tbernard0-GTA/lampform-lab/dist/downloads/reserve_medium/README.txt

LampForm Lab v0.5 / Reserve Medium
Both-part print gate: False
Reserve Medium: abertura equivalente média 6.65 mm; material projetado +12.7%; geometria plana alterada 16.6%. P95 36.0 → 34.3%; P99 45.3 → 48.8%; pico 64.3 → 80.8%; críticos 45 → 44. Gates: TRADE-OFF.
Reserve Medium: abertura equivalente média 6.74 mm; material projetado +8.9%; geometria plana alterada 12.4%. P95 55.5 → 50.9%; P99 70.1 → 79.4%; pico 83.9 → 87.0%; críticos 98 → 93. Gates: PASS.
Units mm. Flat lattice 1 mm, original rim 4 mm. Inspect layers in your slicer. Relative geometric model, not calibrated polymer strain. Mold and Push unchanged. Original source meshes have duplicated faces and are not watertight.
