tbernard0-GTA/lampform-lab/dist/downloads/reserve_search_1/README.txt

LampForm Lab v0.5 / Reserve Search 1
Both-part print gate: False
Reserve Search 1: abertura equivalente média 6.90 mm; material projetado +1.3%; geometria plana alterada 2.7%. P95 36.0 → 32.7%; P99 45.3 → 37.8%; pico 64.3 → 63.0%; críticos 45 → 34. Gates: PASS.
Reserve Search 1: abertura equivalente média 6.91 mm; material projetado +1.0%; geometria plana alterada 2.2%. P95 55.5 → 54.5%; P99 70.1 → 69.9%; pico 83.9 → 84.0%; críticos 98 → 100. Gates: TRADE-OFF.
Units mm. Flat lattice 1 mm, original rim 4 mm. Inspect layers in your slicer. Relative geometric model, not calibrated polymer strain. Mold and Push unchanged. Original source meshes have duplicated faces and are not watertight.
