tbernard0-GTA/lampform-lab/dist/downloads/reserve_search_2/README.txt

LampForm Lab v0.5 / Reserve Search 2
Both-part print gate: False
Reserve Search 2: abertura equivalente média 6.88 mm; material projetado +2.4%; geometria plana alterada 4.2%. P95 36.0 → 35.5%; P99 45.3 → 46.5%; pico 64.3 → 66.9%; críticos 45 → 43. Gates: PASS.
Reserve Search 2: abertura equivalente média 6.89 mm; material projetado +1.7%; geometria plana alterada 3.3%. P95 55.5 → 53.9%; P99 70.1 → 70.3%; pico 83.9 → 85.5%; críticos 98 → 98. Gates: TRADE-OFF.
Units mm. Flat lattice 1 mm, original rim 4 mm. Inspect layers in your slicer. Relative geometric model, not calibrated polymer strain. Mold and Push unchanged. Original source meshes have duplicated faces and are not watertight.
