tbernard0-GTA/lampform-lab/dist/downloads/reserve_search_3/README.txt

LampForm Lab v0.5 / Reserve Search 3
Both-part print gate: True
Reserve Search 3: abertura equivalente média 6.77 mm; material projetado +7.6%; geometria plana alterada 10.9%. P95 36.0 → 29.7%; P99 45.3 → 32.2%; pico 64.3 → 35.1%; críticos 45 → 10. Gates: PASS.
Reserve Search 3: abertura equivalente média 6.82 mm; material projetado +5.3%; geometria plana alterada 8.1%. P95 55.5 → 50.6%; P99 70.1 → 71.2%; pico 83.9 → 84.6%; críticos 98 → 97. Gates: PASS.
Units mm. Flat lattice 1 mm, original rim 4 mm. Inspect layers in your slicer. Relative geometric model, not calibrated polymer strain. Mold and Push unchanged. Original source meshes have duplicated faces and are not watertight.
