tbernard0-GTA/lampform-lab/dist/media/comparisons/peca-1-A_uniform.png

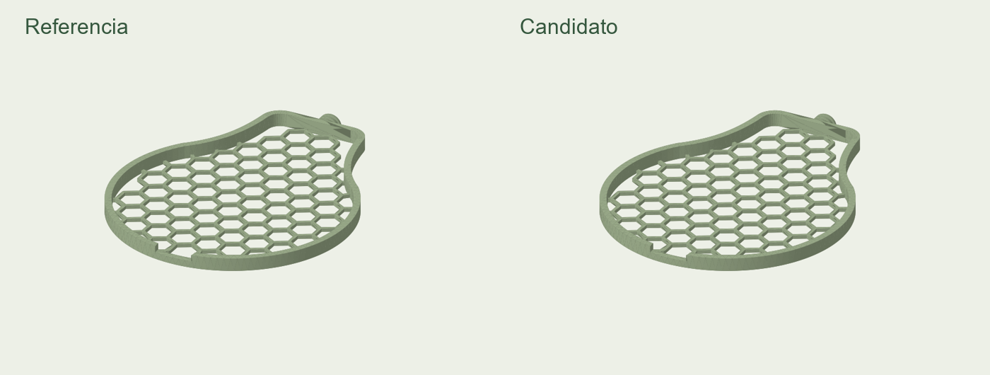
dist/media/comparisons/peca-1-A_uniform.png
