tbernard0-GTA/lampform-lab/dist/media/comparisons/peca-2-A_uniform.png

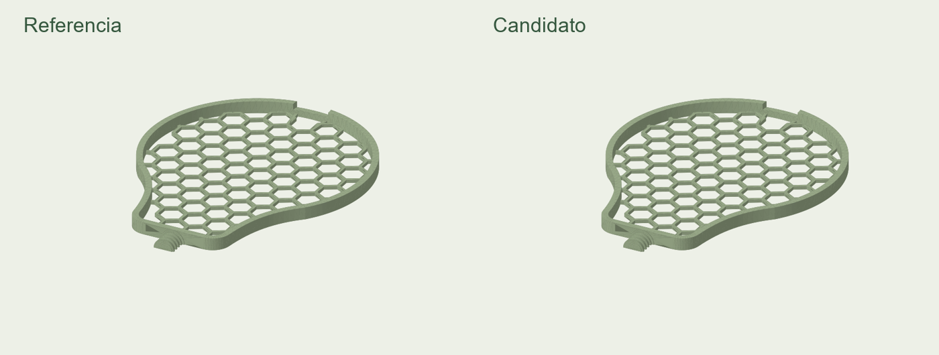
dist/media/comparisons/peca-2-A_uniform.png
