tbernard0-GTA/lampform-lab/docs/video_frames/01_object.png

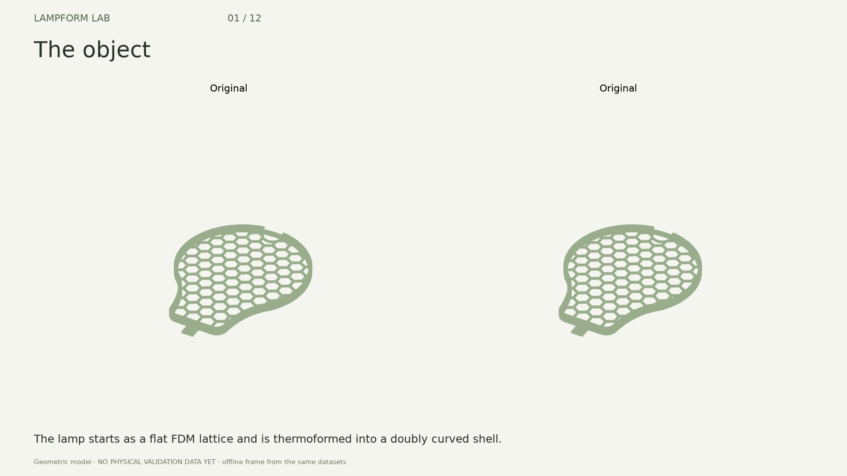
docs/video_frames/01_object.png
