tbernard0-GTA/lampform-lab/docs/video_frames/05_forming.png

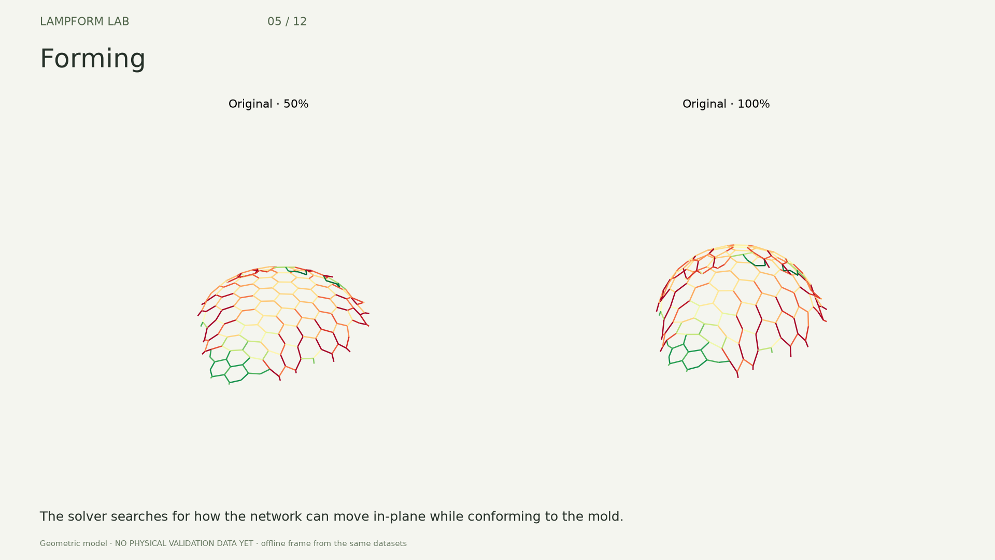
docs/video_frames/05_forming.png
