tbernard0-GTA/lampform-lab/docs/video_frames/06_principal_stretch.png

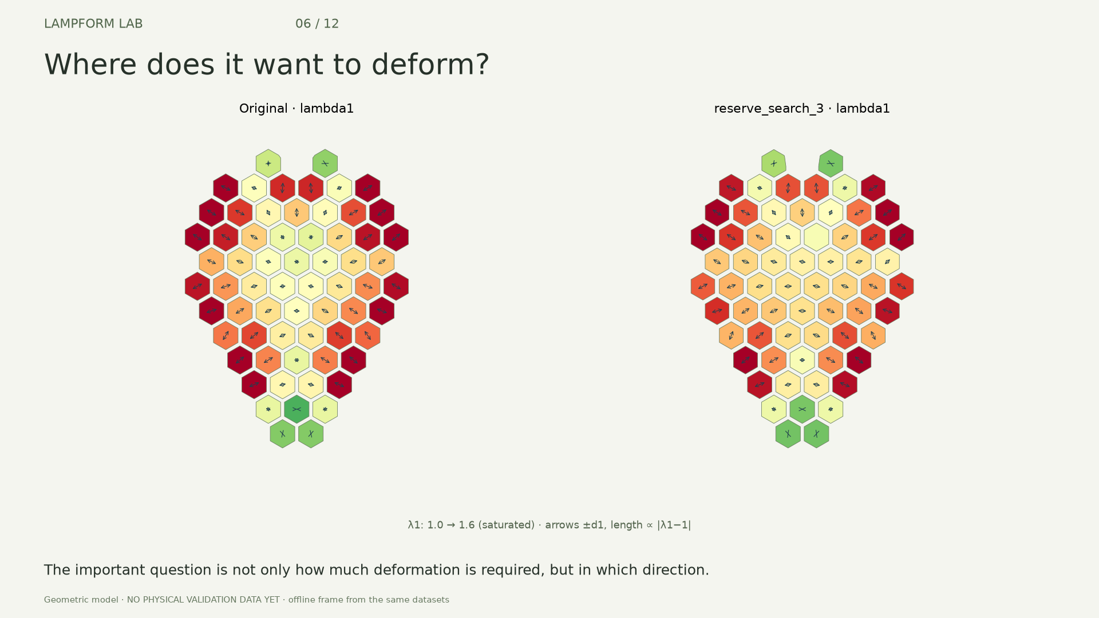
docs/video_frames/06_principal_stretch.png
