tbernard0-GTA/lampform-lab/docs/video_frames/07_mechanisms.png

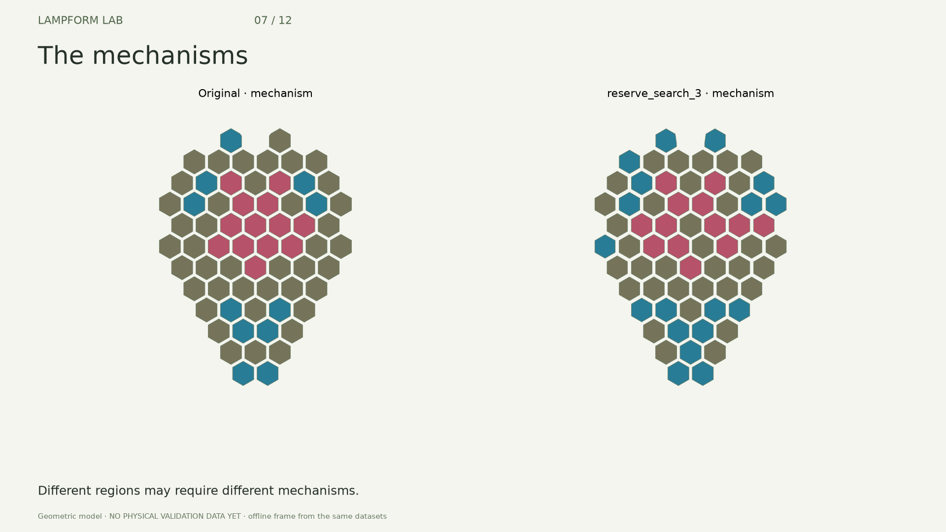
docs/video_frames/07_mechanisms.png
