tbernard0-GTA/lampform-lab/docs/video_frames/12_loop.png

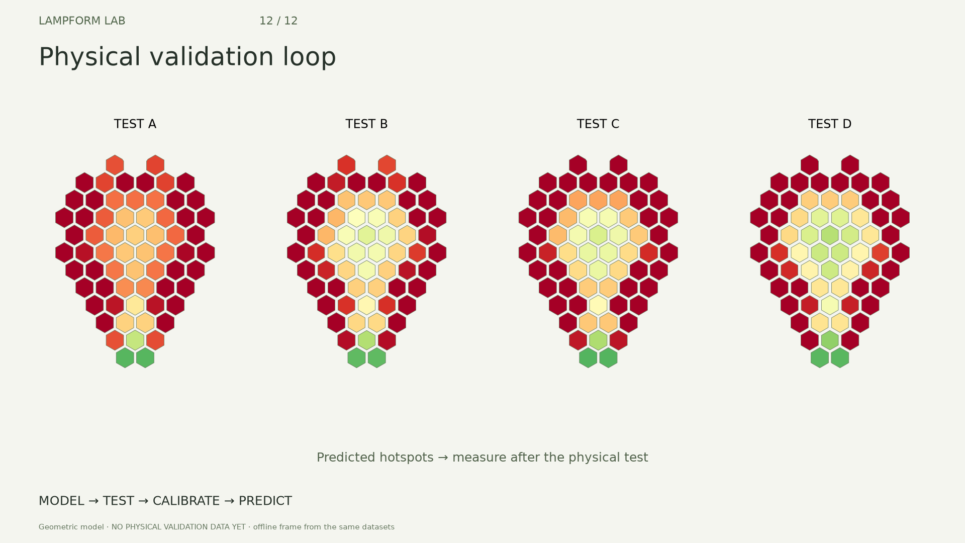
docs/video_frames/12_loop.png
