tbernard0-GTA/lampform-lab/dist/downloads/hybrid_high/HAB-2.stl

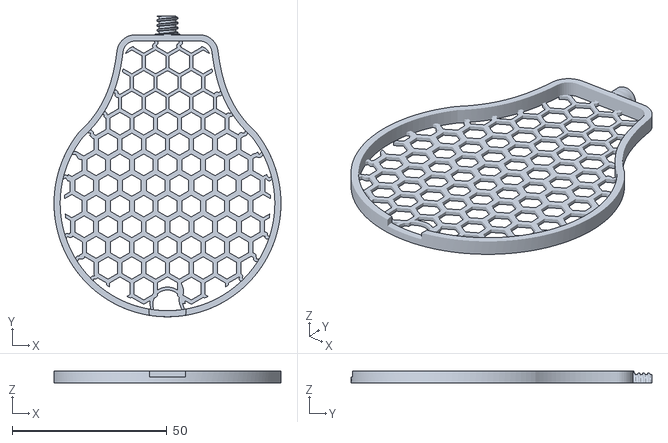
[picture p21: CAD file, 2026-09-14]
dist/downloads/hybrid_high/HAB-2.stl
73.3 x 97.1 x 4.00
