tbernard0-GTA/lampform-lab/dist/downloads/peca-2/peca-2-uniform-w8-h12.stl

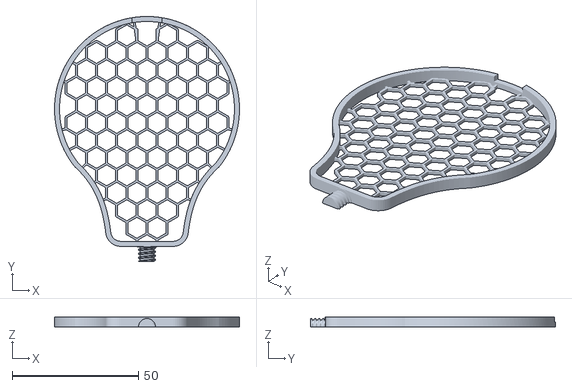
[picture p22: CAD file, 2026-09-14]
dist/downloads/peca-2/peca-2-uniform-w8-h12.stl
73.3 x 97.1 x 4.00
