tbernard0-GTA/lampform-lab/dist/downloads/peca-1/peca-1-uniform-w8-h8.stl

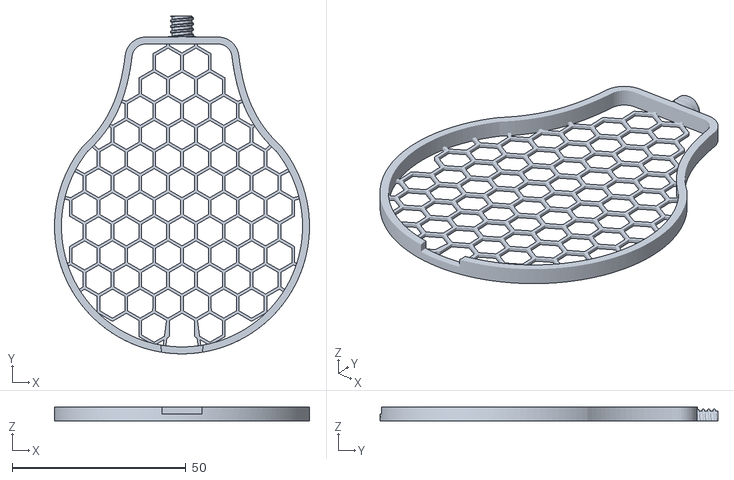
[picture p23: CAD file, 2026-09-14]
dist/downloads/peca-1/peca-1-uniform-w8-h8.stl
73.3 x 97.1 x 4.00
