tbernard0-GTA/lampform-lab/dist/downloads/peca-1/peca-1-comply.stl

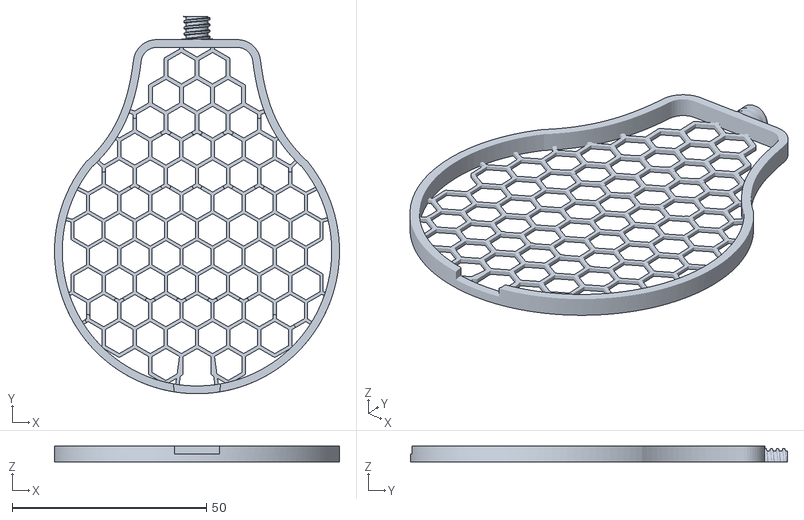
[picture p25: CAD file, 2026-09-14]
dist/downloads/peca-1/peca-1-comply.stl
73.3 x 97.1 x 4.00
