tbernard0-GTA/lampform-lab/dist/downloads/physical-test-v1/ORIGINAL_SUBMERGED.stl

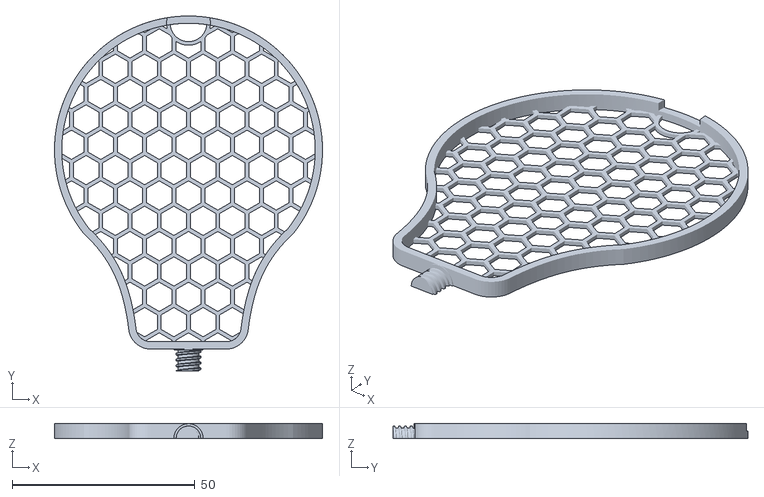
[picture p27: CAD file, 2026-09-14]
dist/downloads/physical-test-v1/ORIGINAL_SUBMERGED.stl
73.3 x 97.1 x 4.00
