tbernard0-GTA/lampform-lab/dist/downloads/peca-1/peca-1-triangle-uniform.stl

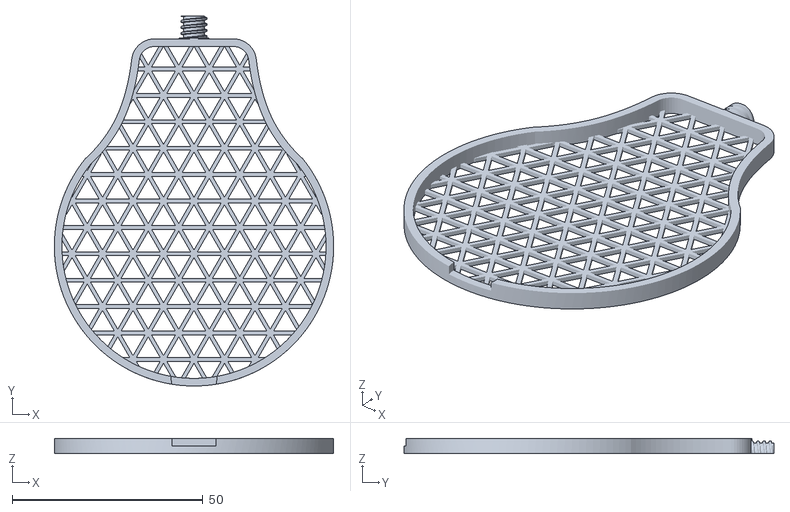
[picture p28: CAD file, 2026-09-14]
dist/downloads/peca-1/peca-1-triangle-uniform.stl
73.3 x 97.1 x 4.00
