tbernard0-GTA/lampform-lab/dist/downloads/peca-1/molde-peca-1.stl

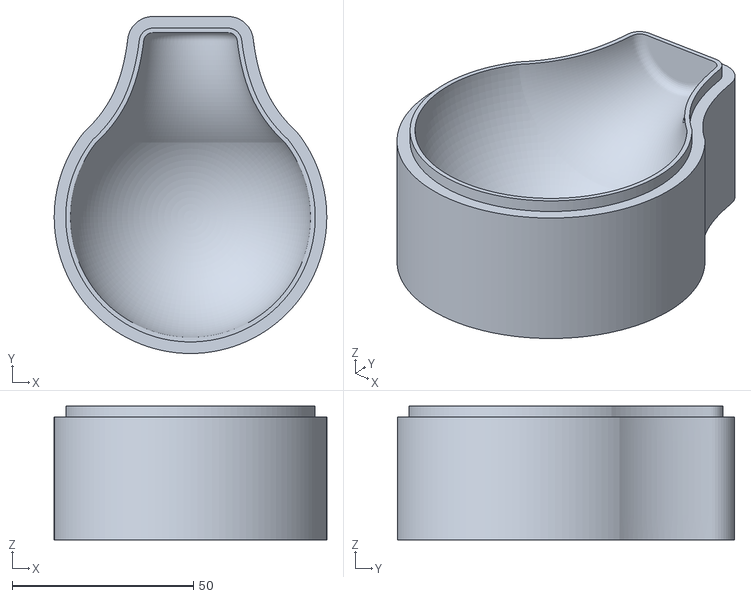
[picture p29: CAD file, 2026-09-14]
dist/downloads/peca-1/molde-peca-1.stl
75.3 x 93.1 x 37.0
