tbernard0-GTA/lampform-lab/dist/downloads/peca-2/molde-peca-2.stl

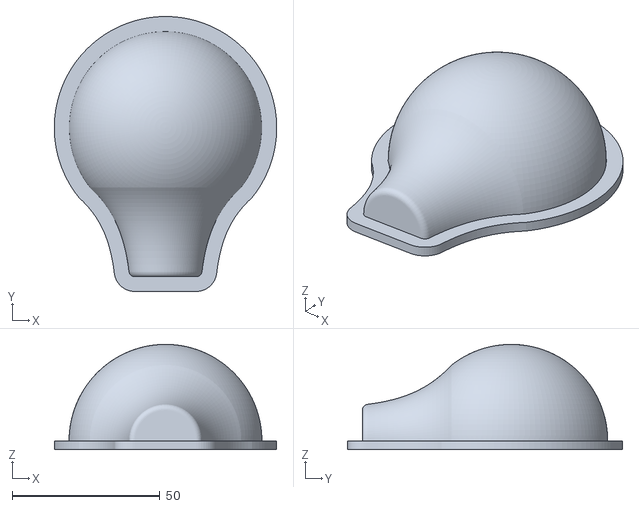
[picture p30: CAD file, 2026-09-14]
dist/downloads/peca-2/molde-peca-2.stl
75.3 x 93.1 x 35.6
