tbernard0-GTA/lampform-lab/docs/video_frames/04_reconstruction.png

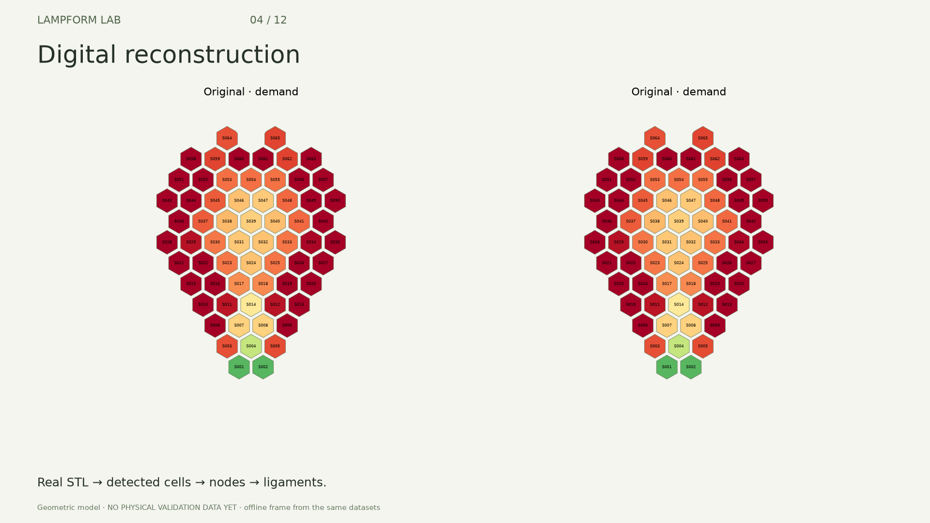
docs/video_frames/04_reconstruction.png
