tbernard0-GTA/lampform-lab/legacy/lampform_lab_v01/results_v02/hab2_mold_ligaments.csv

edge | node_i | node_j | x_i_flat_mm | y_i_flat_mm | x_j_flat_mm | y_j_flat_mm | rest_length_mm | direct_stretch | relaxed_stretch | relaxed_strain_pct | boundary_edge | x_i_relaxed_mm | y_i_relaxed_mm | z_i_relaxed_mm | x_j_relaxed_mm | y_j_relaxed_mm | z_j_relaxed_mm
0 | 0 | 1 | -8.009178843548954 | -36.408438568639944 | -4.009178843548953 | -38.71783964539845 | 4.618802153517008 | 1.1652182478218558 | 1.2637067603260335 | 26.370676032603345 | True | -8.479706115396485 | -38.92221526592342 | 26.563618270766355 | -4.613099313570731 | -40.91395269773462 | 30.456008590282494
1 | 0 | 5 | -8.009178843548954 | -36.408438568639944 | -12.009178843548955 | -38.71783964539845 | 4.6188021535170085 | 2.0815172485556888 | 1.2094080842852 | 20.940808428519997 | True | -8.479706115396485 | -38.92221526592342 | 26.563618270766355 | -11.789339822754865 | -39.16676971053847 | 31.056957788230335
2 | 1 | 2 | -4.009178843548953 | -38.71783964539845 | -4.009178843548953 | -43.33664179891546 | 4.618802153517009 | 2.956658426733236 | 1.4190257372052746 | 41.90257372052746 | True | -4.613099313570731 | -40.91395269773462 | 30.456008590282494 | -4.23444965363972 | -43.77818742922621 | 36.339061376501476
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
