tbernard0-GTA/lampform-lab/legacy/lampform_lab_v01/results_v02/submerged_push_ligaments.csv

edge | node_i | node_j | x_i_flat_mm | y_i_flat_mm | x_j_flat_mm | y_j_flat_mm | rest_length_mm | direct_stretch | relaxed_stretch | relaxed_strain_pct | boundary_edge | x_i_relaxed_mm | y_i_relaxed_mm | z_i_relaxed_mm | x_j_relaxed_mm | y_j_relaxed_mm | z_j_relaxed_mm
0 | 0 | 1 | -4.000001907348633 | -30.55869952494979 | -1.9073486319243216e-06 | -32.86810060170829 | 4.618802153517006 | 1.000001357996387 | 1.0697958023148206 | 6.979580231482063 | False | -4.482262454133736 | -30.31064611485033 | 16.44103529664804 | -0.12099244082813936 | -32.62880514247336 | 16.584821636634377
1 | 0 | 5 | -4.000001907348633 | -30.55869952494979 | -8.000001907348633 | -32.86810060170829 | 4.618802153517005 | 1.148906584055051 | 1.0848531661323328 | 8.485316613233284 | True | -4.482262454133736 | -30.31064611485033 | 16.44103529664804 | -8.042368749836317 | -32.76531476900255 | 13.909715220931664
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
