tbernard0-GTA/lampform-lab/dist/downloads/parametric/hab2/test-v2/A_uniform_height_map.png

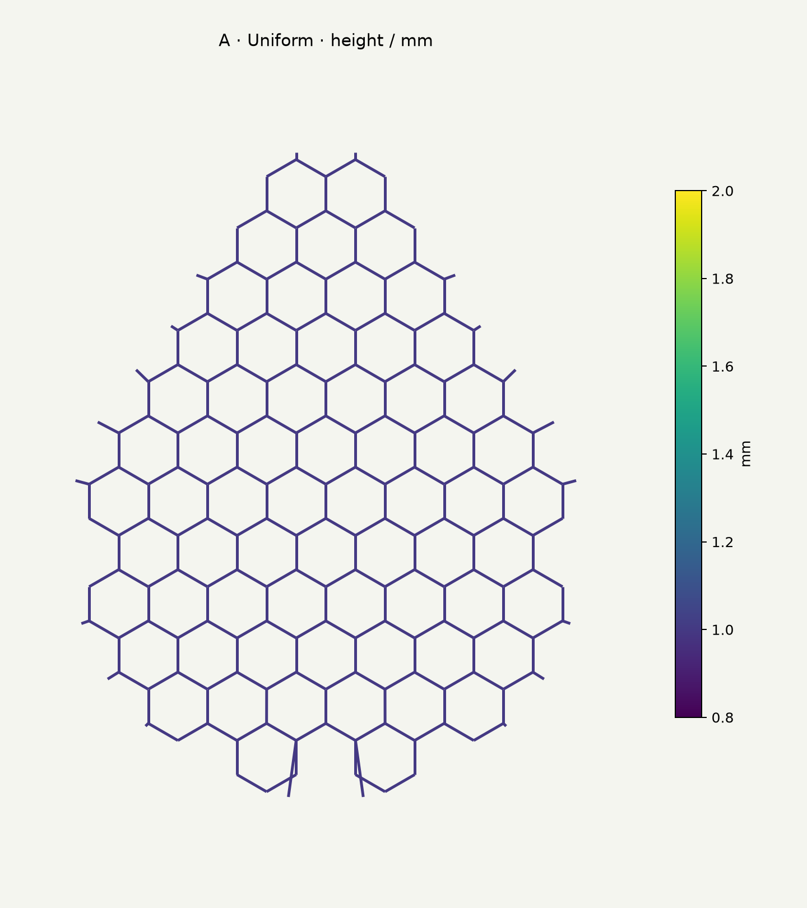
dist/downloads/parametric/hab2/test-v2/A_uniform_height_map.png
