tbernard0-GTA/lampform-lab/dist/downloads/parametric/hab2/test-v2/comparison.png

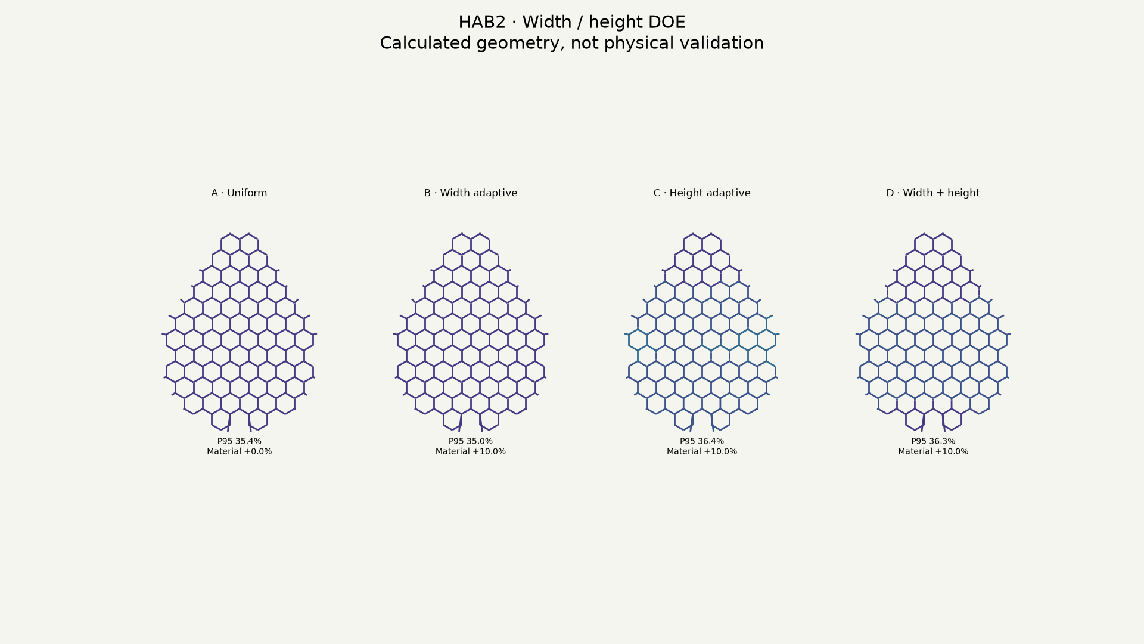
dist/downloads/parametric/hab2/test-v2/comparison.png
