tbernard0-GTA/lampform-lab/dist/downloads/parametric/submerged/test-v2/B_width_width_map.png

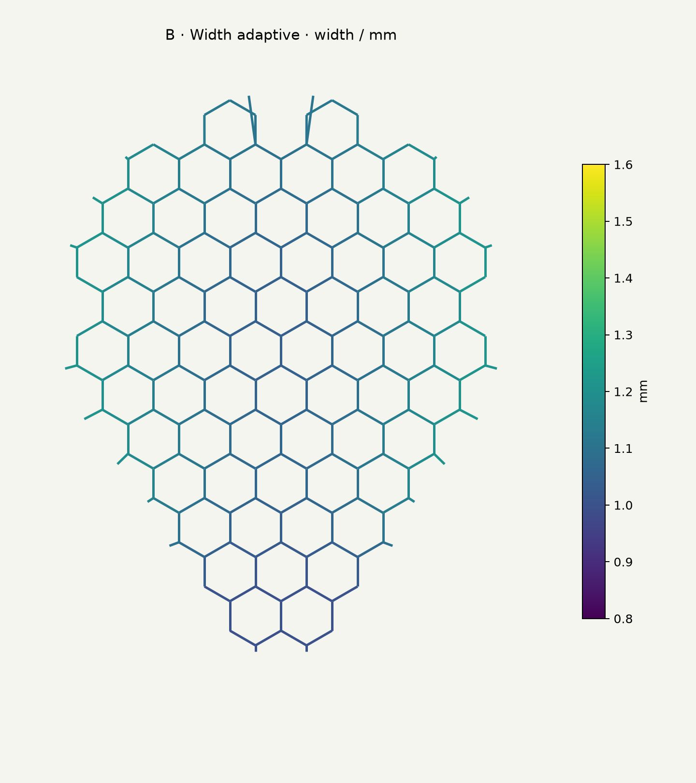
dist/downloads/parametric/submerged/test-v2/B_width_width_map.png
