tbernard0-GTA/lampform-lab/dist/downloads/parametric/submerged/test-v2/D_both_width_map.png

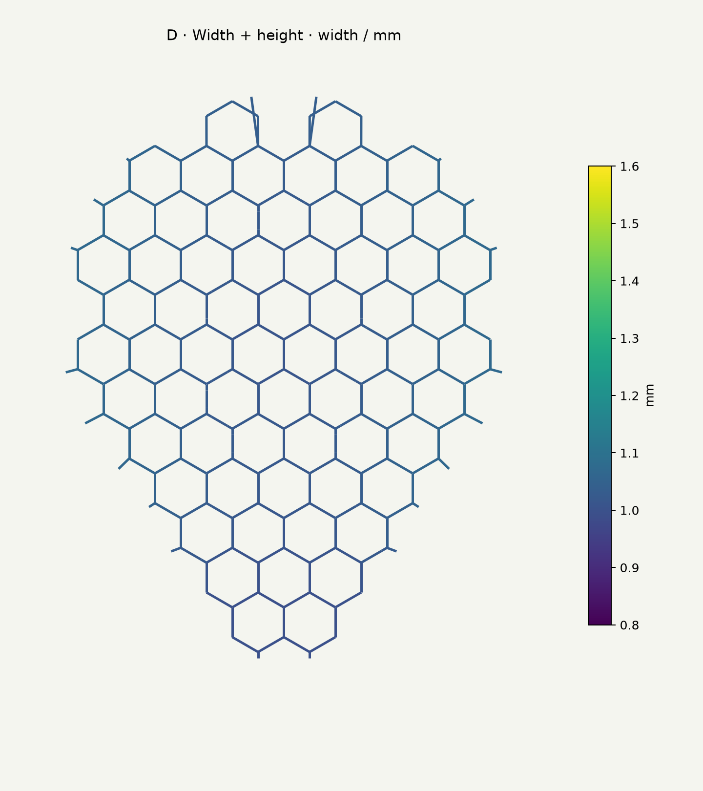
dist/downloads/parametric/submerged/test-v2/D_both_width_map.png
