tbernard0-GTA/lampform-lab/dist/downloads/physical-test-v1/cell_reference_map.png

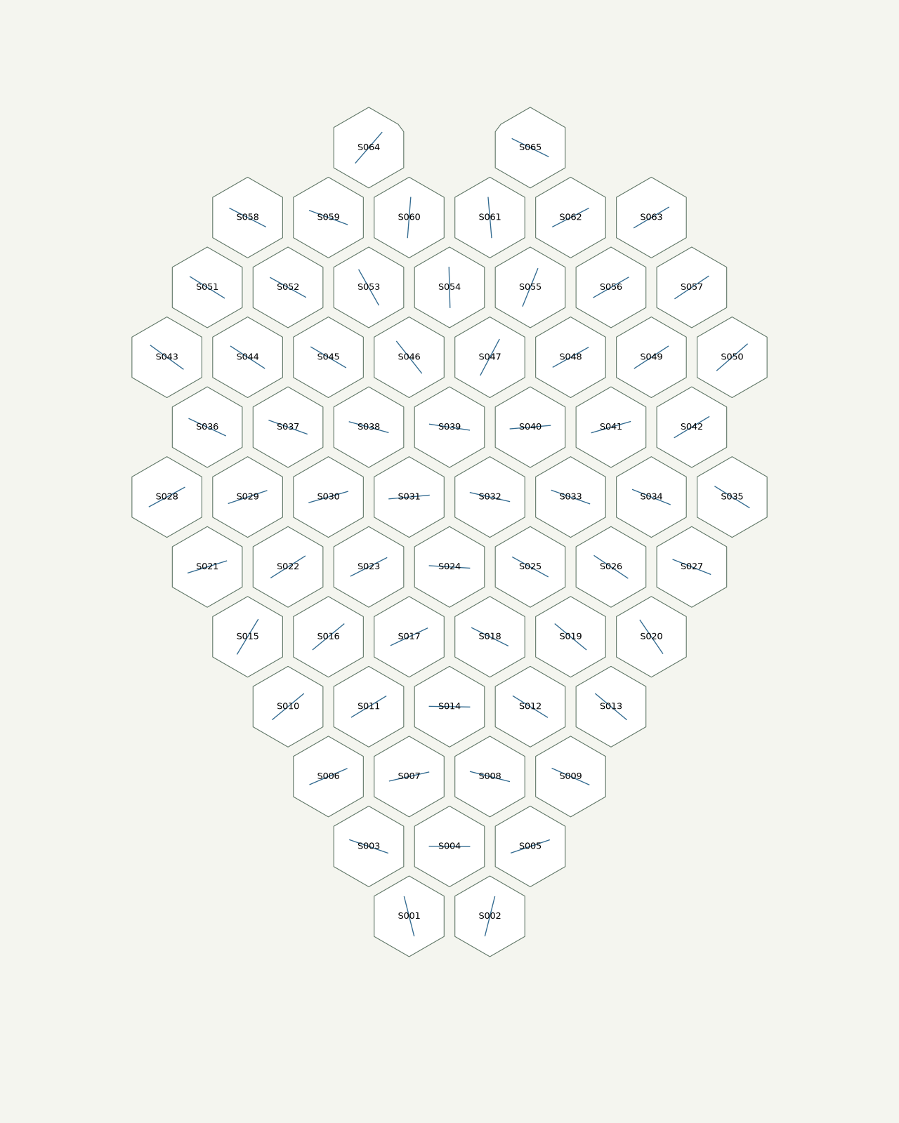
dist/downloads/physical-test-v1/cell_reference_map.png
