tbernard0-GTA/lampform-lab/dist/downloads/physical-test-v1/measurement_plan.png

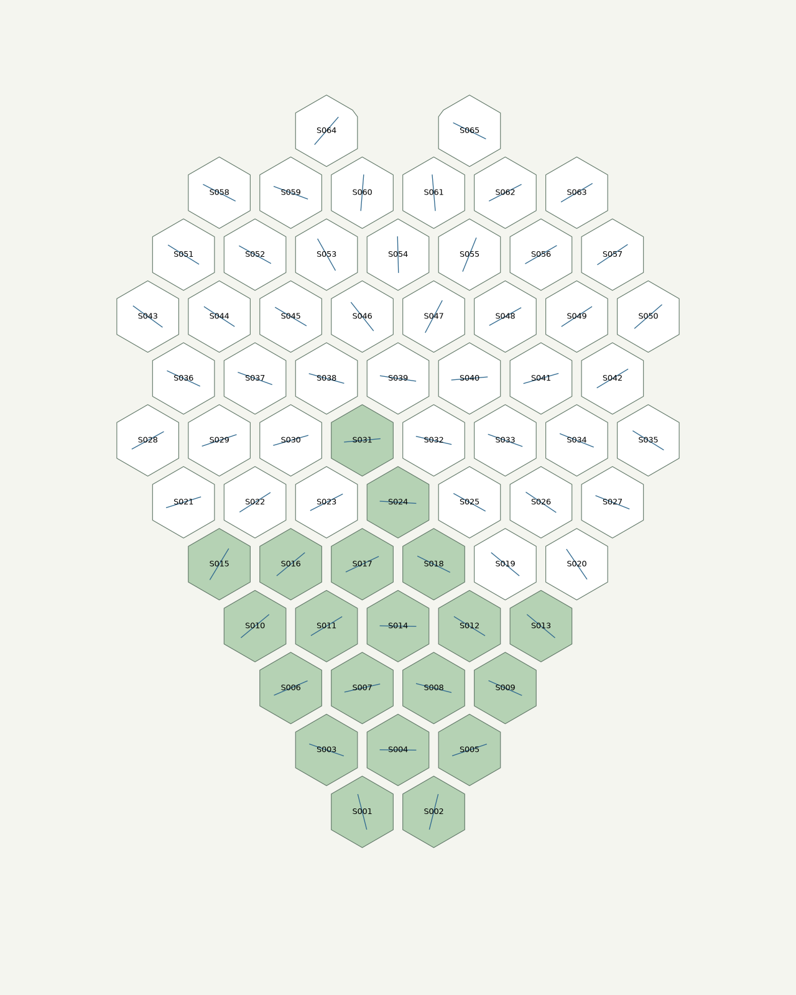
dist/downloads/physical-test-v1/measurement_plan.png
