tbernard0-GTA/lampform-lab/dist/downloads/physical-test-v1/measurement_plan_hab2.png

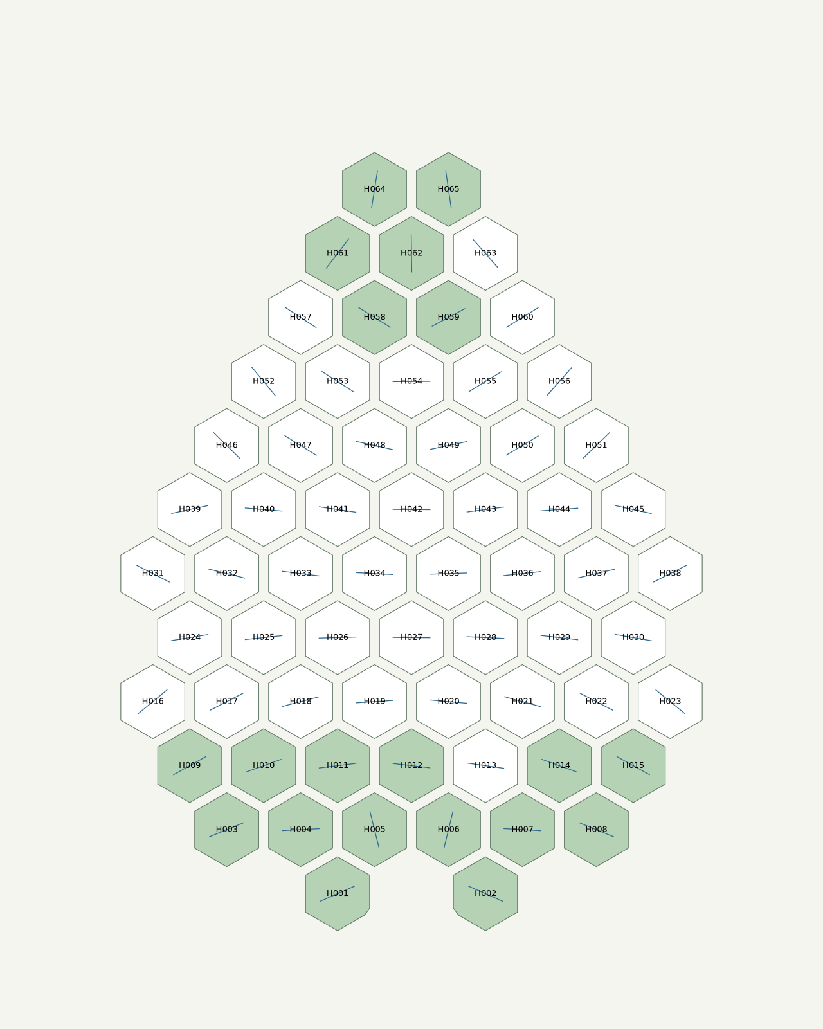
dist/downloads/physical-test-v1/measurement_plan_hab2.png
