tbernard0-GTA/lampform-lab/dist/media/tests/peca-2-A_uniform.png

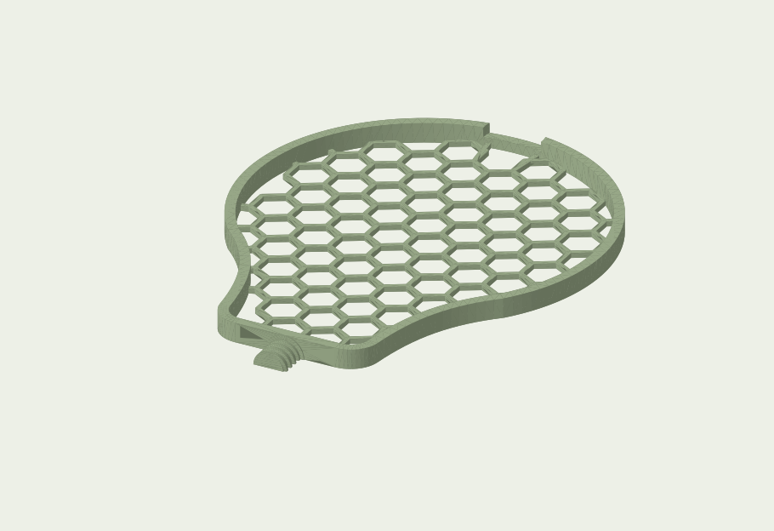
dist/media/tests/peca-2-A_uniform.png
