tbernard0-GTA/lampform-lab/docs/video_frames/08_original_risk.png

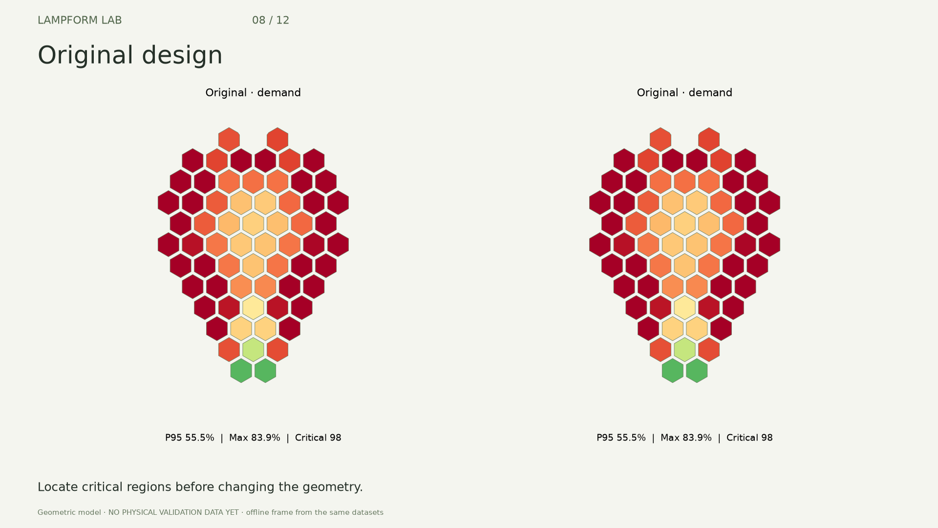
docs/video_frames/08_original_risk.png
